wzgig/220kv-renewable-energy-substation-design/calculations/results/short_circuit/short_circuit_points.csv

point_id | voltage_level | operating_status | normal_operation_status | equivalent_reactance_pu | grid_symmetrical_current_ka | grid_peak_current_ka | grid_short_circuit_capacity_mva | renewable_contribution_status | renewable_minimum_ka | renewable_maximum_ka | conservative_total_maximum_ka | course_total_peak_sensitivity_ka
SC-220-BUS-CLOSED | 220kV | maximum_base_case | conditional_pending_system_parallel_permission | 0.03862059693742504 | 6.499688665509761 | 16.545506151539858 | 2589.2919304697657 | course_current_limited_upper_bound | 0.8111430205156076 | 0.8848832951079354 | 7.384571960617697 | 18.798051274246124
SC-220-I-SEPARATE | 220kV | separate_bus_sensitivity | permitted_separate_operation | 0.06959672337744172 | 3.6068056653765668 | 9.181428279875382 | 1436.8492530556814 | course_current_limited_upper_bound | 0.39037808212123465 | 0.4258669986777105 | 4.032672664054277 | 10.265508673410238
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
