wzgig/220kv-renewable-energy-substation-design/data/design_baseline.yaml

metadata:
  status: "course_design_completed_with_engineering_boundaries"
  date: "2026-07-15"
  change_rule: "revise_only_when_teacher_guidance_or_verified_equipment_data_changes_a_basis"

main_transformers:
  count: 2
  rated_capacity_mva_each: 180
  voltage_ratio_kv: [220, 35]
  winding_type: "two_winding"
  vector_group: "YNd11"
  installation: "outdoor_oil_immersed_on_load_tap_changing"
  short_circuit_voltage_percent: 14
  identifiers: ["T1", "T2"]
  neutral_arrangement: "220kv_star_neutral_directly_grounded_through_neutral_ct; 35kv_delta_winding"

connection_220kv:
  scheme: "single_bus_sectionalized"
  bus_sections: 2
  bypass_bus: false
  bus_tie_breaker: true
  line_circuits_in_service: ["L1", "L2"]
  reserved_line_circuits: ["L3"]
  transformer_bays: ["T1", "T2"]
  normal_bus_tie_state: "open"
  close_permission: "dispatch_authorization_and_synchrocheck_required"
  maximum_short_circuit_bus_tie_state: "closed_conditional_sensitivity"
  healthy_system_parallel_operation: "prohibited_without_dispatch_permission"
  upgrade_trigger: "teacher_requires_bus_maintenance_without_line_or_transformer_outage"
  upgrade_option: "double_bus_without_bypass"

connection_35kv:
  scheme: "single_bus_two_sections"
  equipment_form: "indoor_metal_clad_withdrawable_switchgear"
  bus_tie_normal_state: "open"
  bus_tie_close_condition: "one_source_isolated_and_fault_cleared"
  sections:
    - id: "35kV-I"
      source_transformer: "T1"
      feeder_circuits:
        - {id: "WA-1", source_key: "wind_farm_A", interface: "overhead"}
        - {id: "WA-2", source_key: "wind_farm_A", interface: "overhead"}
        - {id: "WB-1", source_key: "wind_farm_B", interface: "overhead"}
        - {id: "WB-2", source_key: "wind_farm_B", interface: "overhead"}
        - {id: "PVA-1", source_key: "pv_plant_A", interface: "cable"}
        - {id: "PVB-1", source_key: "pv_plant_B", interface: "cable"}
      reserved_bays: 1
      allocated_active_power_mw: 130
    - id: "35kV-II"
      source_transformer: "T2"
      feeder_circuits:
        - {id: "WA-3", source_key: "wind_farm_A", interface: "overhead"}
        - {id: "WA-4", source_key: "wind_farm_A", interface: "overhead"}
        - {id: "WB-3", source_key: "wind_farm_B", interface: "overhead"}
        - {id: "PVA-2", source_key: "pv_plant_A", interface: "cable"}
        - {id: "PVB-2", source_key: "pv_plant_B", interface: "cable"}
        - {id: "ES-1", source_key: "energy_storage", interface: "cable"}
      reserved_bays: 1
      allocated_active_power_mw: 140
  auxiliary_transformer_bays:
    - {id: "T10-1-HV", transformer: "T10-1", source_section: "35kV-I", rated_capacity_mva: 31.5, rating_status: "provisional_frozen_for_course_design"}
    - {id: "T10-2-HV", transformer: "T10-2", source_section: "35kV-II", rated_capacity_mva: 31.5, rating_status: "provisional_frozen_for_course_design"}

connection_10kv:
  scheme: "single_bus_two_sections"
  bus_tie_normal_state: "open"
  bus_tie_close_condition: "one_35_10_5kv_source_isolated_and_fault_cleared"
  healthy_sources_parallel_operation: "prohibited"
  source_transformers:
    count: 2
    voltage_ratio_kv: [35, 10.5]
    short_circuit_voltage_percent: 8
    rated_capacity_mva_each: 31.5
    identifiers: ["T10-1", "T10-2"]
    vector_group: "YNd11"
    neutral_arrangement: "35kv_star_neutral_not_used_for_system_grounding; 10_5kv_delta_winding"
    source_bays_35kv: ["T10-1-HV", "T10-2-HV"]
    source_sections_35kv: ["35kV-I", "35kV-II"]
    type_envelope: "35kv_oil_immersed_power_transformer"
    exact_model_status: "pending_41C_environment_and_grounding_review"
    rated_current_a: {35kv: 519.615, 10_5kv: 1732.051}
  reactive_compensation:
    status: "provisional_frozen_for_course_design"
    technology: "dynamic_svg"
    target_power_factor: 0.98
    inverter_reactive_headroom_credited: false
    calculated_required_mvar_35kv_only: 21.3029
    calculated_required_mvar_conservative_with_10kv_auxiliary: 21.8875
    total_dynamic_range_mvar: [-24, 24]
    units:
      - {id: "SVG-1", rated_range_mvar: [-12, 12], rated_mvar: 12, source_section: "10kV-I"}
      - {id: "SVG-2", rated_range_mvar: [-12, 12], rated_mvar: 12, source_section: "10kV-II"}
    harmonic_study_status: "pending"
    exact_vendor_model_status: "pending"
  load_allocation_status: "frozen_two_symmetric_sections_with_one_svg_each"

connection_0_4kv:
  scheme: "single_bus_sectionalized"
  system: "380_220V_three_phase_four_wire"
  bus_tie_normal_state: "closed"
  standby_mode: "dark_standby_mutual_alternate"
  normal_transformers_in_service: 1
  normal_incomer_state: "one_closed_one_open"
  normal_operation: "one_transformer_supplies_both_bus_sections_through_closed_bus_tie"
  transfer_operation: "isolate_failed_incomer_then_close_standby_transformer_incomer_bus_tie_remains_closed"
  station_service_transformers:
    count: 2
    rated_capacity_kva_each: 200
    voltage_ratio_kv: [10, 0.4]
    identifiers: ["TS1", "TS2"]
    source_sections: ["10kV-I", "10kV-II"]
    type: "SCB14_dry_type_cast_resin"
    vector_group: "Dyn11"
    short_circuit_voltage_percent: 4

operating_modes:
  normal:
    active_220kv_lines: ["L1", "L2"]
    active_main_transformers: ["T1", "T2"]
    reserved_220kv_lines: ["L3"]
    bus_ties:
      220kv: "open"
      35kv: "open"
      10kv: "open"
      0_4kv: "closed_under_single_transformer_operation"
    station_service_transformers:
      active_count: 1
      standby_count: 1
      rotation: "alternate_by_operation_schedule"
  main_transformer_n_minus_one:
    action_sequence:
      - "isolate_faulted_main_transformer"
      - "close_35kv_bus_tie_only_after_fault_clearance"
      - "curtail_renewable_output_to_no_more_than_180MVA_through_surviving_transformer"
      - "retain_10kv_and_0_4kv_important_loads"
    required_curtailment_percent_baseline: 35.7798
  one_220kv_line_out:
    action: "remaining_line_carries_export_subject_to_LGJ_400_50_temperature_corrected_ampacity"
    full_export_current_a_approx: 735.559
    course_reference_ampacity_at_41c_a: 475.242
    line_only_required_curtailment_percent: 35.390
    interaction_with_main_transformer_n_minus_one: "main_transformer_35_780_percent_curtailment_is_slightly_more_restrictive_and_reduces_line_current_to_about_472_377A"
  220kv_bus_tie_transfer:
    conservative_continuous_duty_a: 735.559
    basis: "one energized section transfers the full pre-curtailment export duty before operating limits are applied"
  auxiliary_source_n_minus_one:
    action_10kv: "isolate_failed_35_10_5kv_source_then_close_10kv_bus_tie_after_fault_clearance"
    full_svg_range_retained: true
    worst_case_transformer_loading_percent: 79.166
    priority: "retain_station_service_control_communications_and_cooling_then_coordinate_svg_output_with_voltage_and_transformer_limits"
    action_0_4kv: "isolate_failed_station_service_incomer_then_close_standby_transformer_incomer_with_0_4kv_bus_tie_remaining_closed"
  prohibited:
    - "parallel_operation_of_system_1_and_system_2_through_220kv_bus_tie_without_dispatch_permission_and_synchrocheck"
    - "parallel_operation_of_two_healthy_main_transformers_through_closed_35kv_bus_tie"
    - "parallel_operation_of_two_healthy_T10_transformers_through_closed_10kv_bus_tie"

site_conditions:
  altitude_m_max: 1000
  altitude_status: "course_design_assumption"
  pollution_level: "d"
  pollution_status: "conservative_course_design_assumption"
  indoor_switchgear_max_temperature_c: 40
  indoor_temperature_basis: "ventilation_and_air_conditioning_keep_the_switchgear_room_within_normal_service_temperature_despite_41C_outdoor_maximum"

neutral_grounding:
  220kv: "direct_grounding"
  35kv: "grounding_transformer_plus_low_resistance_course_assumption"
  10kv: "grounding_transformer_plus_low_resistance_course_assumption"
  35kv_ground_fault_current_a: 400
  35kv_resistor_ohm_approx: 50.5
  35kv_short_time_s: 10
  10kv_ground_fault_current_a: 200
  10kv_resistor_ohm_approx: 28.9
  10kv_short_time_s: 10
  sectionalized_source_scheme:
    normal:
      35kv: {bus_tie: "open", sources_in_service: ["GT35-I", "GT35-II"], rule: "one_grounding_source_per_energized_section"}
      10kv: {bus_tie: "open", sources_in_service: ["GT10-I", "GT10-II"], rule: "one_grounding_source_per_energized_section"}
    bus_tie_transfer:
      sequence:
        - "isolate_the_faulted_or_receiving_section_grounding_source_before_bus_tie_closure"
        - "verify_only_the_healthy_source_side_grounding_transformer_resistor_set_remains_in_service"
        - "close_bus_tie_only_after_the_grounding_source_interlock_permissive_is_true"
      prohibited: "bus_tie_closed_with_two_section_grounding_sources_connected_in_parallel"
    sectionalized_restoration: "open_bus_tie_then_restore_one_grounding_source_on_each_energized_section"
  equipment_packages:
    35kv:
      quantity: 2
      identifiers: ["GT35-I", "GT35-II"]
      connection: "ZN_neutral_forming"
      rated_ground_fault_current_a: 400
      duration_s: 10
      resistor_ohm_approx: 50.5
      selected_capacity_kva_each: 1000
    10kv:
      quantity: 2
      identifiers: ["GT10-I", "GT10-II"]
      connection: "ZN_neutral_forming"
      rated_ground_fault_current_a: 200
      duration_s: 10
      resistor_ohm_approx: 28.9
      selected_capacity_kva_each: 200
  status: "taskbook_grounding_category_satisfied; low_resistance_values_are_course_design_selections_pending_protection_and_vendor_coordination"

protection_and_thermal_duty:
  main_protection_operating_s: 0.05
  backup_protection_operating_s: 1.00
  breaker_intrinsic_opening_s: 0.04
  breaker_total_clearing_s: 0.08
  contact_separation_s: 0.09
  thermal_equivalent_duration_s: 1.10
  status: "course_design_assumption_pending_final_coordination_and_exact_device_data"

switchyard_220kv:
  arrangement: "outdoor_AIS_phase_segregated_medium_type"
  plan_sheet: {format: "A1", orientation: "landscape", scale: "1:200"}
  section_sheet: {format: "A1", orientation: "landscape", scale: "1:100"}
  line_bay_detail_sheet: {format: "A1", orientation: "landscape", scale: "1:50", drawing_id: "SEC-220-L1-01"}
  plan_site_size_m: [145, 90]
  normal_road_width_m: 4
  phase_spacing_m: 4
  typical_function_center_pitch_m: 14
  bus_support_span_for_course_mechanical_check_m: 8
  bus_support_span_status: "conservative_course_mechanical_assumption_pending_manufacturer_support_design"
  line_bus_to_gantry_m: 29
  transformer_bus_to_gantry_m: 20
  transformer_bus_to_center_m: 27
  bus_conductor_elevation_m: 9
  line_gantry_conductor_elevation_m: 14.5
  transformer_gantry_conductor_elevation_m: 11.5
  minimum_clearances_mm:
    A1: 1800
    A2: 2000
    B1: 2550
    B2: 1900
    C: 4300
    D: 3800
  course_source: "chapter_7_table_7_2_page_13_220J_column"
  final_standard_review: "DL_T_5352_2018_full_text_required_for_construction_use"

open_engineering_inputs:
  - "L3_role_and_expected_in_service_date"
  - "teacher_reliability_requirement_for_220kv_bus_maintenance"
  - "final_LGJ_400_50_manufacturer_thermal_rating_with_defined_weather_conditions"
  - "final_reactive_power_voltage_harmonic_and_svg_short_circuit_study"
  - "T10_and_outdoor_SVG_exact_vendor_models_for_41C_service"
  - "indoor_35kv_10kv_switchgear_exact_vendor_models_for_controlled_40C_room"
