wzgig/220kv-renewable-energy-substation-design/drawings/data/switchyard_layout.yaml

schema_version: 1
drawing_set_id: "SWYD-220-AIS-01"
standard_ref: "../standards/switchyard_standard.yaml"
baseline_ref: "../../data/design_baseline.yaml"

common:
  voltage_level_kv: 220
  highest_voltage_kv: 252
  arrangement: "outdoor_AIS_phase_segregated_medium_type"
  altitude_m_max: 1000
  pollution_level: "d"
  phase_spacing_m: 4.0
  typical_function_center_pitch_m: 14.0
  normal_road_width_m: 4.0
  plan_site_size_m: [145, 90]
  bus_conductor_elevation_m: 9.0
  line_gantry_conductor_elevation_m: 14.5
  transformer_gantry_conductor_elevation_m: 11.5
  minimum_clearances_mm: {A1: 1800, A2: 2000, B1: 2550, B2: 1900, C: 4300, D: 3800}
  clearance_evidence: "course_chapter_7_table_7_2_page_13_220J_column"
  final_standard_review: "DL_T_5352_2018_full_text_required_for_construction_use"
  geometry_status: "course_design_engineering_base_not_construction_setting_out"

device_envelopes:
  circuit_breaker:
    plan_footprint_m: [3.2, 2.8]
    terminal_elevation_m: 5.5
    evidence_class: "course_geometry_assumption_pending_exact_vendor_outline"
  disconnector:
    plan_footprint_m: [3.6, 2.4]
    terminal_elevation_m: 6.0
    evidence_class: "course_geometry_assumption_pending_exact_vendor_outline"
  current_transformer:
    plan_footprint_m: [2.2, 2.2]
    terminal_elevation_m: 5.0
    evidence_class: "course_geometry_assumption_pending_exact_vendor_outline"
  cvt:
    plan_footprint_m: [2.2, 2.2]
    terminal_elevation_m: 5.2
    evidence_class: "course_geometry_assumption_pending_exact_vendor_outline"
  surge_arrester:
    plan_footprint_m: [1.8, 1.8]
    terminal_elevation_m: 5.0
    evidence_class: "course_geometry_assumption_pending_exact_vendor_outline"
  main_transformer:
    plan_footprint_m: [14.0, 10.0]
    highest_bushing_elevation_m: 7.5
    evidence_class: "course_geometry_assumption_pending_exact_180MVA_vendor_outline"

plan:
  drawing_id: "LAY-220-01"
  drawing_title: "220kV户外AIS配电装置平面布置图"
  sheet: {format: "A1", orientation: "landscape", width: 841, height: 594, scale: 200, scale_label: "1:200"}
  paper_origin_mm: [45, 90]
  site_boundary_m: [0, 0, 145, 90]
  fence_inset_m: 2
  ais_area_m: [8, 16, 137, 85]
  roads:
    - {id: "perimeter-road", bounds_m: [5, 16, 140, 85], width_m: 4, kind: "loop"}
    - {id: "transformer-road", bounds_m: [34, 19, 104, 23], width_m: 4, kind: "straight"}
  bus_sections:
    - {id: "BUS-220-I", section: "220kV-I", x_m: [10, 60], center_y_m: 55}
    - {id: "BUS-220-II", section: "220kV-II", x_m: [74, 135], center_y_m: 55}
  bus_tie: {id: "220-BS", x_m: [60, 74], center_y_m: 55, normal_state: "open"}
  line_bays:
    - {id: "L1", section: "220kV-I", center_x_m: 18, bus_y_m: 55, gantry_y_m: 84, status: "in_service", direction: "northwest", label: "系统1线路 L1\n70km LGJ-400/50"}
    - {id: "L2", section: "220kV-II", center_x_m: 109, bus_y_m: 55, gantry_y_m: 84, status: "in_service", direction: "northwest", label: "系统2线路 L2\n85km LGJ-400/50"}
    - {id: "L3", section: "220kV-II", center_x_m: 123, bus_y_m: 55, gantry_y_m: 84, status: "reserved", direction: "northwest", label: "预留线路 L3\n60km LGJ-400/50"}
  transformer_bays:
    - {id: "T1", section: "220kV-I", center_x_m: 32, bus_y_m: 55, gantry_y_m: 35, transformer_center_m: [32, 28], label: "1号主变 T1"}
    - {id: "T2", section: "220kV-II", center_x_m: 95, bus_y_m: 55, gantry_y_m: 35, transformer_center_m: [95, 28], label: "2号主变 T2"}
  bus_voltage_transformers:
    - {id: "PT-220-I", section: "220kV-I", center_m: [46, 48], label: "I段CVT/PT"}
    - {id: "PT-220-II", section: "220kV-II", center_m: [81, 48], label: "II段CVT/PT"}
  buildings:
    - {id: "CTRL", bounds_m: [8, 4, 22, 15], label: "主控通信楼"}
    - {id: "MVSWGR", bounds_m: [108, 4, 138, 15], label: "35/10kV配电楼\n含T10与SVG区域"}
  section_marks:
    - {id: "A-A", axis: "y", coordinate_m: 18, ranges_m: [[28, 52], [58, 82]], label: "线路间隔断面 A-A"}
    - {id: "B-B", axis: "y", coordinate_m: 32, ranges_m: [[24, 50]], label: "主变间隔断面 B-B"}
  notes:
    - "本图按A1、1:200绘制，北向上；220kV线路向西北出线。"
    - "220kV采用户外AIS分相中型布置，单母线分段；分段断路器正常断开。"
    - "母线相间距4.0m、间隔几何和设备轮廓为课程设计值；安全净距不得小于表列A1/A2/B1/B2/C/D。"
    - "L3及其间隔为远期预留；35/10kV采用室内开关柜，在配电楼内布置。"
    - "精确基础、端子方向、设备外形、爬距和运输转弯半径待厂家图覆盖；电气净距施工前按DL/T 5352-2018正文复核。"

sections:
  drawing_id: "SEC-220-01"
  drawing_title: "220kV户外AIS典型间隔断面图"
  sheet: {format: "A1", orientation: "landscape", width: 841, height: 594, scale: 100, scale_label: "1:100"}
  panels:
    - id: "A-A"
      title: "线路间隔断面 A-A"
      paper_origin_mm: [50, 155]
      width_m: 34
      ground_elevation_m: 0
      equipment_sequence:
        - {id: "BUS-SUPPORT", kind: "bus_support", x_m: 2, terminal_elevation_m: 9.0, label: "管形母线"}
        - {id: "DS-BUS", kind: "disconnector", x_m: 6, terminal_elevation_m: 6.0, label: "母线侧隔离开关"}
        - {id: "CB", kind: "circuit_breaker", x_m: 10, terminal_elevation_m: 5.5, label: "SF6断路器"}
        - {id: "CT", kind: "current_transformer", x_m: 14, terminal_elevation_m: 5.0, label: "电流互感器"}
        - {id: "DS-LINE", kind: "disconnector", x_m: 18, terminal_elevation_m: 6.0, earthing_switch: true, label: "线路侧隔离开关+常开ES"}
        - {id: "CVT", kind: "cvt", x_m: 22, terminal_elevation_m: 5.2, label: "CVT"}
        - {id: "LA", kind: "surge_arrester", x_m: 25, terminal_elevation_m: 5.0, label: "避雷器"}
        - {id: "LINE-GANTRY", kind: "line_gantry", x_m: 31, terminal_elevation_m: 14.5, label: "出线构架"}
    - id: "B-B"
      title: "主变间隔断面 B-B"
      paper_origin_mm: [430, 155]
      width_m: 34
      ground_elevation_m: 0
      equipment_sequence:
        - {id: "BUS-SUPPORT", kind: "bus_support", x_m: 2, terminal_elevation_m: 9.0, label: "管形母线"}
        - {id: "DS-BUS", kind: "disconnector", x_m: 6, terminal_elevation_m: 6.0, label: "母线侧隔离开关"}
        - {id: "CB", kind: "circuit_breaker", x_m: 10, terminal_elevation_m: 5.5, label: "SF6断路器"}
        - {id: "CT", kind: "current_transformer", x_m: 14, terminal_elevation_m: 5.0, label: "电流互感器"}
        - {id: "LA", kind: "surge_arrester", x_m: 18, terminal_elevation_m: 5.0, label: "避雷器"}
        - {id: "TX-GANTRY", kind: "transformer_gantry", x_m: 22, terminal_elevation_m: 11.5, label: "主变构架"}
        - {id: "T1", kind: "main_transformer", x_m: 29, terminal_elevation_m: 7.5, label: "180MVA主变"}
  notes:
    - "断面标高以场地±0.000为基准；尺寸单位为m，电气净距表单位为mm。"
    - "无遮栏裸导体对地C≥4.30m；本图最低主要带电端子标高5.00m。"
    - "相间距采用4.00m，分别大于A2=2.00m与课程检修布置要求。"
    - "设备高度与占位为课程几何假设，正式工程必须由厂家外形图、端子荷载和基础图覆盖。"
    - "课程设计假设：海拔≤1000m、污秽d级；超过1000m或污区更严时重新校核绝缘与净距。"
    - "净距表采用课程第七章表7-2的220J列；正式工程或施工前必须按DL/T 5352-2018正文复核。"

line_bay_detail:
  drawing_id: "SEC-220-L1-01"
  drawing_title: "220kV I段L1线路间隔断面详图"
  sheet: {format: "A1", orientation: "landscape", width: 841, height: 594, scale: 50, scale_label: "1:50"}
  paper_origin_mm: [65, 120]
  width_m: 34
  ground_elevation_m: 0
  grounding_grid_elevation_m: -0.8
  equipment_sequence:
    - {id: "BUS-SUPPORT", equipment_no: "220-L1-BUS", kind: "bus_support", x_m: 2, terminal_elevation_m: 9.0, label: "220kV I段Φ100/90管母"}
    - {id: "DS-BUS", equipment_no: "220-L1-QS1", kind: "disconnector", x_m: 6, terminal_elevation_m: 6.0, label: "母线侧QS"}
    - {id: "CB", equipment_no: "220-L1-QF", kind: "circuit_breaker", x_m: 10, terminal_elevation_m: 5.5, label: "SF6断路器QF"}
    - {id: "CT", equipment_no: "220-L1-TA", kind: "current_transformer", x_m: 14, terminal_elevation_m: 5.0, label: "电流互感器TA"}
    - {id: "DS-LINE", equipment_no: "220-L1-QS2/ES", kind: "disconnector", x_m: 18, terminal_elevation_m: 6.0, earthing_switch: true, label: "线路侧QS+ES(NO)"}
    - {id: "CVT", equipment_no: "220-L1-CVT", kind: "cvt", x_m: 22, terminal_elevation_m: 5.2, label: "电容式电压互感器CVT"}
    - {id: "LA", equipment_no: "220-L1-MOA", kind: "surge_arrester", x_m: 25, terminal_elevation_m: 5.0, label: "金属氧化物避雷器MOA"}
    - {id: "LINE-GANTRY", equipment_no: "220-L1-G", kind: "line_gantry", x_m: 31, terminal_elevation_m: 14.5, label: "出线构架"}
  parameter_rows:
    - ["系统/绝缘", "Un=220kV；Um=252kV；LIWV=950kV"]
    - ["QF课程目标", "252kV；3150A；50kA(3s)；峰值125kA"]
    - ["QS课程目标", "252kV；3150A；50kA(3s)；峰值125kA"]
    - ["TA/CVT", "TA=1000/1A；CVT=220/√3kV / 100/√3V，另保护及100/3V开口三角；二次负荷/准确级组合待复核"]
    - ["MOA", "YH10W-204/532；Uc=159kV；In=10kA"]
    - ["导体/净距", "Φ100/90铝合金管母；相间4.0m；A1/A2/C见图"]
  notes:
    - "本图为L1单间隔课程设计详图，设备外形、基础和端子荷载须由最终厂家图覆盖。"
    - "线路侧QS配常开ES，并与QF、QS设置机械/电气防误联锁；检修接地须按操作票执行。"
    - "地下接地网与设备/构架接地仅作连接示意；接地电阻、接触电压和跨步电压尚需专项计算。"
    - "MOA用于限制雷电及操作过电压；本图不代表全站避雷针/避雷线直击雷保护范围已完成。"
